hackffm/ESP32S3_OLED_Eyes/attic/walle1.h

//const unsigned int sampleRate = 22050;
const unsigned int wav_len = 21760;

// array size is 21760
const unsigned char walle_wav[]  = {
  0x32, 0xfe, 0x6d, 0xfd, 0xb3, 0xfa, 0x82, 0xfa, 0xab, 0xfb, 0x3f, 0xfb, 0xc0, 0xfe, 0xe3, 0xfe, 
  0x04, 0x01, 0x0f, 0x03, 0x01, 0x04, 0xe7, 0x06, 0x82, 0x08, 0x4c, 0x08, 0x78, 0x07, 0x09, 0x05, 
  0x69, 0x01, 0x1c, 0xfe, 0xb0, 0xf9, 0xdb, 0xf6, 0x6c, 0xf5, 0xb2, 0xf2, 0x41, 0xf3, 0x00, 0xf5, 
  0x5a, 0xf5, 0xc9, 0xf9, 0xc3, 0xfc, 0xce, 0x00, 0x94, 0x06, 0xaa, 0x07, 0x92, 0x0b, 0xe3, 0x0b, 
  0x1b, 0x0b, 0x31, 0x0d, 0xaf, 0x09, 0x02, 0x0a, 0x82, 0x08, 0x7e, 0x04, 0x42, 0x04, 0x5c, 0xff, 
  0xab, 0xfc, 0x45, 0xfb, 0x36, 0xf6, 0xec, 0xf6, 0x0b, 0xf5, 0xad, 0xf4, 0x86, 0xf8, 0xd2, 0xf8, 
  0x0b, 0xfe, 0xee, 0x02, 0xa2, 0x06, 0xff, 0x0b, 0xfe, 0x0c, 0xfb, 0x0d, 0xdf, 0x0c, 0x61, 0x09, 
  0x7d, 0x07, 0xae, 0x04, 0xa8, 0x02, 0x2b, 0x02, 0x71, 0x01, 0x00, 0x00, 0x27, 0x00, 0xd5, 0xfd, 
  0x38, 0xfc, 0x19, 0xfa, 0x05, 0xf8, 0xd4, 0xf7, 0x1e, 0xf6, 0xe1, 0xf7, 0xa6, 0xf9, 0x54, 0xfc, 
  0xee, 0xff, 0x2d, 0x01, 0xa7, 0x03, 0xf7, 0x02, 0xdd, 0x01, 0x7c, 0x02, 0xd6, 0xff, 0xbe, 0x00, 
  0x32, 0x00, 0x9c, 0xff, 0x7f, 0x01, 0x9d, 0x00, 0x1b, 0x02, 0xc6, 0x01, 0x01, 0x01, 0x06, 0x03, 
  0x7e, 0x02, 0x15, 0x03, 0x90, 0x04, 0x89, 0x03, 0x9a, 0x03, 0xea, 0x02, 0xd7, 0xfe, 0x9e, 0xfe, 
  0x5b, 0xfb, 0x99, 0xf7, 0xef, 0xf8, 0x2f, 0xf4, 0xd8, 0xf6, 0xb0, 0xf7, 0x63, 0xf6, 0xb3, 0xfc, 
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
  0x8e, 0x03, 0x27, 0xff, 0x8c, 0xfa, 0x97, 0xf7, 0x63, 0xf5, 0xf9, 0xf5, 0x21, 0xf7, 0x56, 0xf9, 
  0xba, 0xfc, 0x9a, 0xfe, 0xc8, 0x01, 0x45, 0x02, 0x6a, 0x01, 0x58, 0x01, 0x79, 0xfd, 0x49, 0xfc, 
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
};
