hackffm/ESP32S3_OLED_Eyes/attic/MyCreds.h

// Sample for MyCreds.h
// Place this file in .platformio/lib/MyCreds/MyCreds.h (create folders if necessary)
// Then PlatformIO will find it, but your credentials does not go to GIT.
#ifndef WIFI_SSID
#define WIFI_SSID "SSID_HERE"
#define WIFI_PASSWORD "PASSWORD_HERE"
#endif
